Ramkomak/oil_furnace_control/PCB/Oli_furnace/Oli_furnace.kicad_pcb

## KiCad design hardware/MyRepeater-ESP32-ETH.kicad_sch

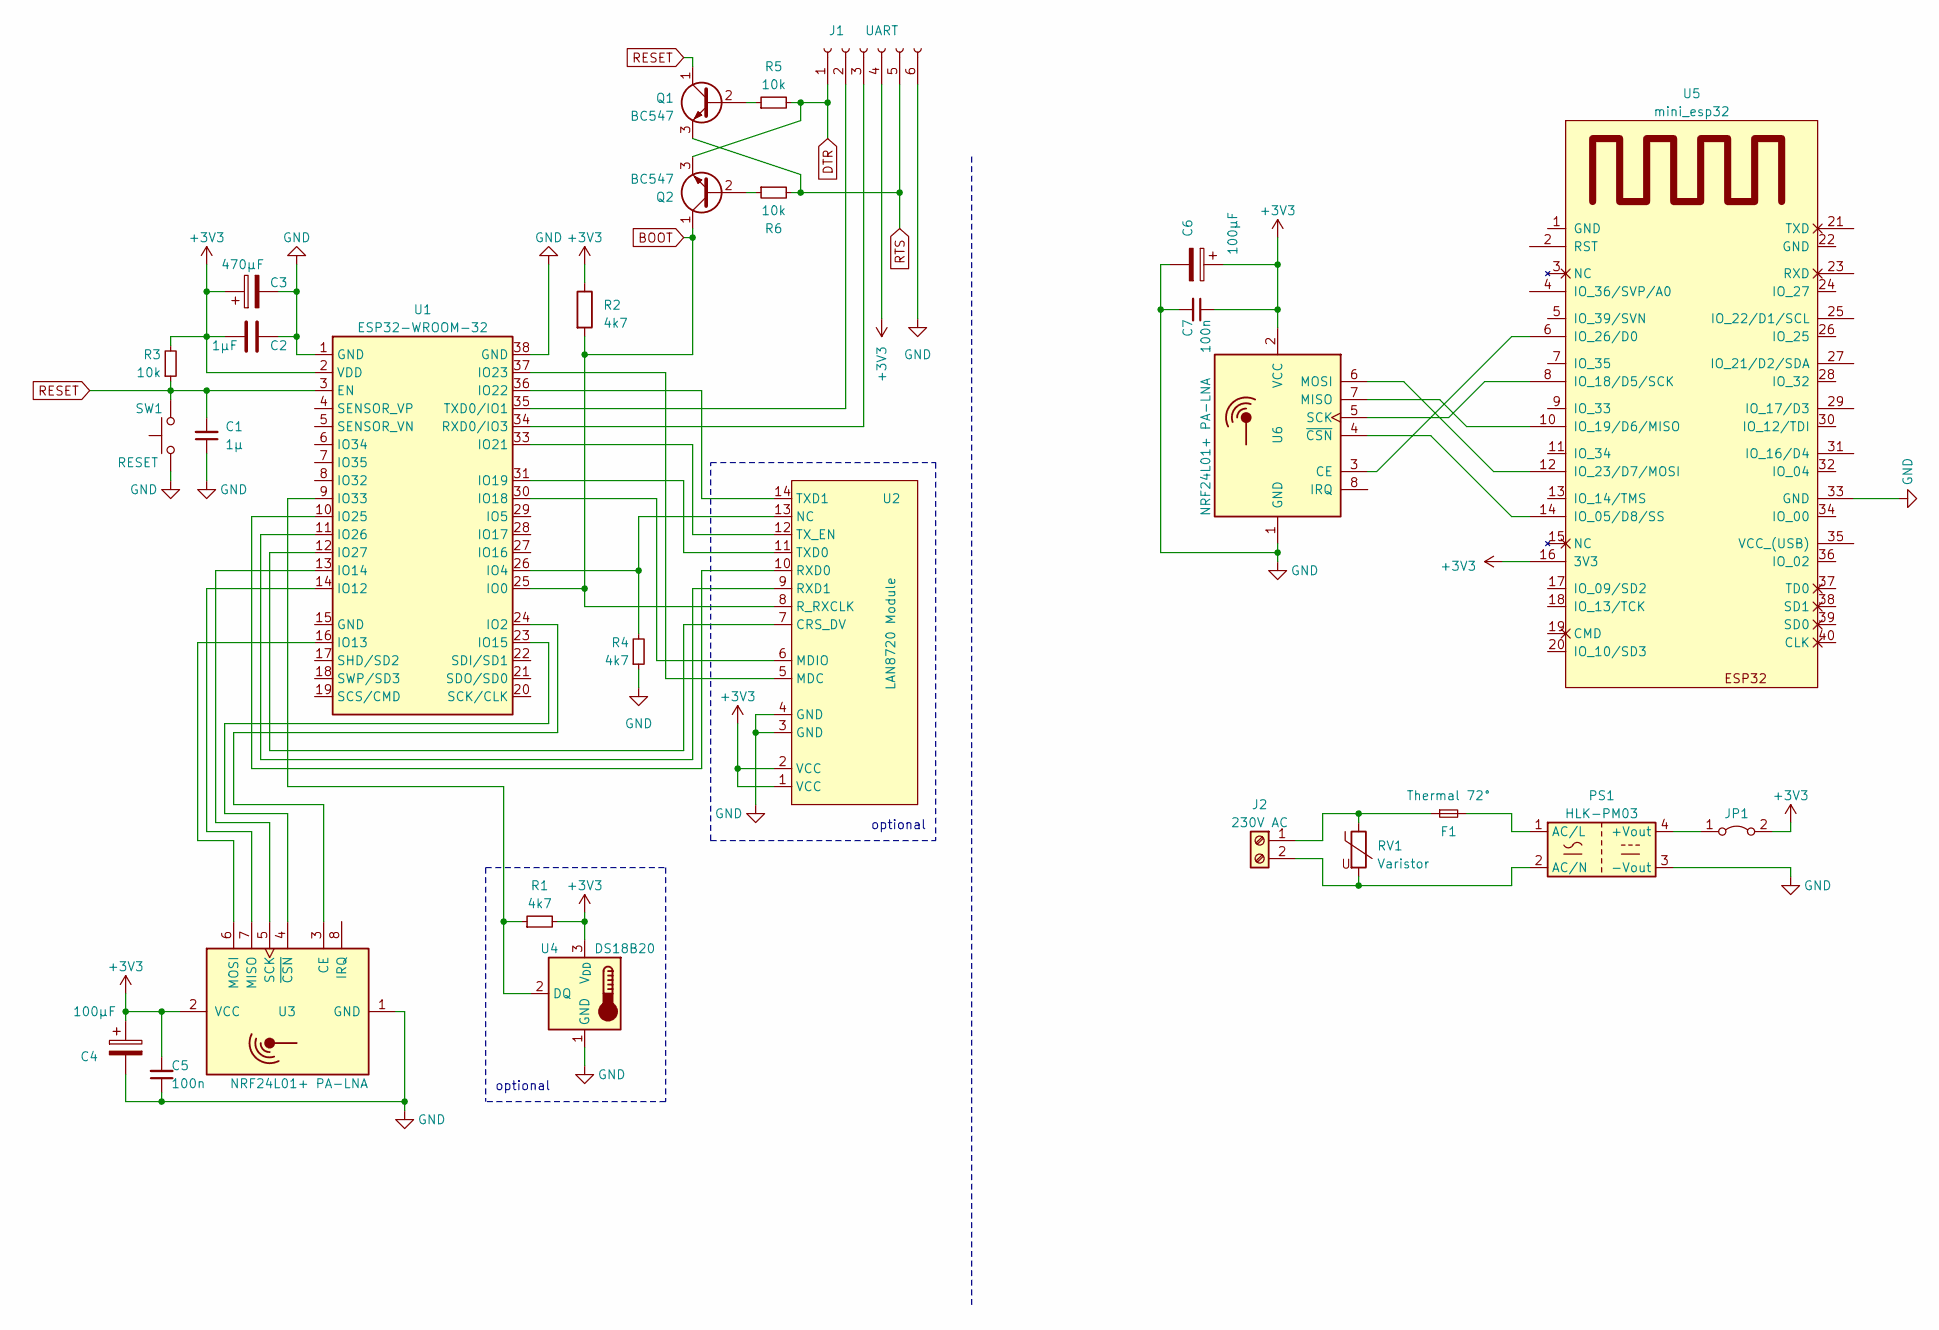
[picture p8: schematic MyRepeater-ESP32-ETH.kicad_sch]

Parts:
C1: 1µ
C2: 1µF
C3: 470µF
C4, C6: 100µF
C5, C7: 100n
F1: Thermal 72°
J1: UART
J2: 230V AC
JP1: Jumper_2_Bridged
PS1: HLK-PM03; Converter_ACDC_HiLink_HLK-PMxx
Q1, Q2: BC547; TO-92_Inline
R1, R2, R4: 4k7
R3, R5, R6: 10k
RV1: Varistor
SW1: RESET
U1: ESP32-WROOM-32
U2: LAN8720 Module
U3, U6: NRF24L01+ PA-LNA; nRF24L01_Breakout
U4: DS18B20; TO-92_Inline
U5: mini_esp32

Connections:
+3V3: C2.1, C3.1, C4.1, C5.2, C6.1, C7.1, J1.4, JP1.2 (B), R1.2, R2.1, R3.2, U1.2 (VDD), U2.1 (VCC), U2.2 (VCC), U3.2 (VCC), U4.3 (V_{DD}), U5.16 (3V3), U6.2 (VCC)
BOOT: Q2.1 (C), R2.2, U1.25 (IO0), U2.8 (R_RXCLK)
DTR: J1.1, Q2.3 (E), R5.2
GND: C1.1, C2.2, C3.2, C4.2, C5.1, C6.2, C7.2, J1.6, PS1.3 (-Vout), R4.1, SW1.1, U1.1 (GND), U1.38 (GND), U2.3 (GND), U2.4 (GND), U3.1 (GND), U4.1 (GND), U5.33 (GND), U6.1 (GND)
unnamed: F1.1, J2.1, RV1.1
unnamed: F1.2, PS1.1 (AC/L)
unnamed: J1.2, U1.35 (TXD0/IO1)
unnamed: J1.3, U1.34 (RXD0/IO3)
unnamed: J2.2, PS1.2 (AC/N), RV1.2
unnamed: JP1.1 (A), PS1.4 (+Vout)
unnamed: Q1.2 (B), R5.1
unnamed: Q2.2 (B), R6.1
unnamed: R1.1, U1.9 (IO33), U4.2 (DQ)
unnamed: R4.2, U1.26 (IO4), U2.13 (NC)
unnamed: U1.10 (IO25), U2.10 (RXD0)
unnamed: U1.11 (IO26), U2.9 (RXD1)
unnamed: U1.12 (IO27), U2.7 (CRS_DV)
unnamed: U1.13 (IO14), U3.5 (SCK)
unnamed: U1.14 (IO12), U3.7 (MISO)
unnamed: U1.16 (IO13), U3.6 (MOSI)
unnamed: U1.23 (IO15), U3.4 (~CSN)
unnamed: U1.24 (IO2), U3.3 (CE)
unnamed: U1.30 (IO18), U2.6 (MDIO)
unnamed: U1.31 (IO19), U2.11 (TXD0)
unnamed: U1.33 (IO21), U2.12 (TX_EN)
unnamed: U1.36 (IO22), U2.14 (TXD1)
unnamed: U1.37 (IO23), U2.5 (MDC)
unnamed: U5.6 (IO_26/D0), U6.3 (CE)
unnamed: U5.8 (IO_18/D5/SCK), U6.5 (SCK)
unnamed: U5.10 (IO_19/D6/MISO), U6.7 (MISO)
unnamed: U5.12 (IO_23/D7/MOSI), U6.6 (MOSI)
unnamed: U5.14 (IO_05/D8/SS), U6.4 (~CSN)
RESET: C1.2, Q1.1 (C), R3.1, SW1.2, U1.3 (EN)
RTS: J1.5, Q1.3 (E), R6.2

Notes on the sheet:
optional
