Ramkomak/oil_furnace_control/web_server/htmldata.c

static const unsigned char data_index_shtml[] = {
	/* ./index.shtml */
	0x2f, 0x69, 0x6e, 0x64, 0x65, 0x78, 0x2e, 0x73, 0x68, 0x74, 0x6d, 0x6c, 0,
	0x48, 0x54, 0x54, 0x50, 0x2f, 0x31, 0x2e, 0x30, 0x20, 0x32, 
	0x30, 0x30, 0x20, 0x4f, 0x4b, 0x0d, 0x0a, 0x53, 0x65, 0x72, 
	0x76, 0x65, 0x72, 0x3a, 0x20, 0x6c, 0x77, 0x49, 0x50, 0x2f, 
	0x70, 0x72, 0x65, 0x2d, 0x30, 0x2e, 0x36, 0x20, 0x28, 0x68, 
	0x74, 0x74, 0x70, 0x3a, 0x2f, 0x2f, 0x77, 0x77, 0x77, 0x2e, 
	0x73, 0x69, 0x63, 0x73, 0x2e, 0x73, 0x65, 0x2f, 0x7e, 0x61, 
	0x64, 0x61, 0x6d, 0x2f, 0x6c, 0x77, 0x69, 0x70, 0x2f, 0x29, 
	0x0d, 0x0a, 0x43, 0x6f, 0x6e, 0x74, 0x65, 0x6e, 0x74, 0x2d, 
	0x74, 0x79, 0x70, 0x65, 0x3a, 0x20, 0x74, 0x65, 0x78, 0x74, 
	0x2f, 0x68, 0x74, 0x6d, 0x6c, 0x0d, 0x0a, 0x0d, 0x0a, 
	0x3c, 0x21, 0x44, 0x4f, 0x43, 0x54, 0x59, 0x50, 0x45, 0x20, 
	0x68, 0x74, 0x6d, 0x6c, 0x3e, 0x0a, 0x3c, 0x68, 0x74, 0x6d, 
	0x6c, 0x3e, 0x0a, 0x20, 0x20, 0x20, 0x20, 0x3c, 0x68, 0x65, 
	0x61, 0x64, 0x3e, 0x20, 0x0a, 0x20, 0x20, 0x20, 0x20, 0x20, 
	0x20, 0x20, 0x20, 0x3c, 0x74, 0x69, 0x74, 0x6c, 0x65, 0x3e, 
	0x4f, 0x69, 0x6c, 0x20, 0x46, 0x75, 0x72, 0x6e, 0x61, 0x63, 
	0x65, 0x3c, 0x2f, 0x74, 0x69, 0x74, 0x6c, 0x65, 0x3e, 0x20, 
	0x0a, 0x20, 0x20, 0x20, 0x20, 0x20, 0x20, 0x20, 0x20, 0x3c, 
	0x6d, 0x65, 0x74, 0x61, 0x20, 0x6e, 0x61, 0x6d, 0x65, 0x3d, 
	0x22, 0x76, 0x69, 0x65, 0x77, 0x70, 0x6f, 0x72, 0x74, 0x22, 
	0x20, 0x63, 0x6f, 0x6e, 0x74, 0x65, 0x6e, 0x74, 0x3d, 0x22, 
	0x77, 0x69, 0x64, 0x74, 0x68, 0x3d, 0x64, 0x65, 0x76, 0x69, 
	0x63, 0x65, 0x2d, 0x77, 0x69, 0x64, 0x74, 0x68, 0x2c, 0x20, 
	0x69, 0x6e, 0x69, 0x74, 0x69, 0x61, 0x6c, 0x2d, 0x73, 0x63, 
	0x61, 0x6c, 0x65, 0x3d, 0x31, 0x22, 0x3e, 0x0a, 0x20, 0x20, 
	0x20, 0x20, 0x3c, 0x2f, 0x68, 0x65, 0x61, 0x64, 0x3e, 0x0a, 
	0x20, 0x20, 0x20, 0x20, 0x3c, 0x62, 0x6f, 0x64, 0x79, 0x3e, 
	0x20, 0x3c, 0x68, 0x31, 0x3e, 0x4f, 0x69, 0x6c, 0x20, 0x46, 
	0x75, 0x72, 0x6e, 0x61, 0x63, 0x65, 0x3c, 0x2f, 0x68, 0x31, 
	0x3e, 0x0a, 0x20, 0x20, 0x20, 0x20, 0x20, 0x20, 0x20, 0x20, 
	0x3c, 0x62, 0x72, 0x3e, 0x0a, 0x20, 0x20, 0x20, 0x20, 0x20, 
	0x20, 0x20, 0x20, 0x3c, 0x68, 0x32, 0x3e, 0x49, 0x6e, 0x66, 
	0x6f, 0x3a, 0x3c, 0x2f, 0x68, 0x32, 0x3e, 0x0a, 0x20, 0x20, 
	0x20, 0x20, 0x20, 0x20, 0x20, 0x20, 0x3c, 0x70, 0x3e, 0x4f, 
	0x69, 0x6c, 0x20, 0x74, 0x65, 0x6d, 0x70, 0x3a, 0x20, 0x3c, 
	0x21, 0x2d, 0x2d, 0x23, 0x74, 0x65, 0x6d, 0x70, 0x2d, 0x2d, 
	0x3e, 0x43, 0x3c, 0x2f, 0x70, 0x3e, 0x0a, 0x20, 0x20, 0x20, 
	0x20, 0x20, 0x20, 0x20, 0x20, 0x3c, 0x70, 0x3e, 0x53, 0x74, 
	0x61, 0x74, 0x75, 0x73, 0x3a, 0x20, 0x3c, 0x21, 0x2d, 0x2d, 
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
	};

const struct fsdata_file file_index_shtml[] = {{ NULL, data_index_shtml, data_index_shtml + 13, sizeof(data_index_shtml) - 13, FS_FILE_FLAGS_HEADER_INCLUDED | FS_FILE_FLAGS_HEADER_PERSISTENT}};

#define FS_ROOT file_index_shtml
#define FS_NUMFILES 1
